yangshunhuai/C4-Clock/software/src/PeriphControl.cpp

#include <Arduino.h>
#include "C4-Clock.h"

void beep() {
	digitalWrite(BUZZER, HIGH);
	delay(100);
	digitalWrite(BUZZER, LOW);
}

char waitForKeypad() {
	keypadEvent e;
	while (1) {
		keypad.tick();
		if (keypad.available()) {
			e = keypad.read();
			if (e.bit.EVENT == KEY_JUST_RELEASED) break;
		}
	}
	beep();
	char serbuf[7];
	sprintf(serbuf, "%c down", e.bit.KEY);
	Serial.println(serbuf);
	return e.bit.KEY;
}

int getIntFromKeypad(int bits, int echoRow, int echoCol) {
	String number;
	for (int i = 0; i <= (bits - 1); i++) {
		char key = '\0';
		do
		{
			key = waitForKeypad();
		} while (key == 'A' || key == 'B' || key == 'C' || key == 'D' || key == '*' || key == '#');
		lcd.setCursor(echoCol + i, echoRow);
		lcd.print(key);
		number += key;
	}
	char serbuf[30];
	sprintf(serbuf, "Got %i from keypad", number.toInt());
	Serial.println(serbuf);
	return number.toInt();
}
