yangshunhuai/C4-Clock/software/include/Settings.h

void settings();
void setAlarm();
void setNet();
void setEffect();
void about();
void resetConfig();
void saveTimeCfg(struct timeConfig* configStruct);
void getAlarmCfg(struct alarmConfig *configStruct);
void saveAlarmCfg(struct alarmConfig *configStruct);
